KHesemeyer88/SDP/data/marcus_triangle.png

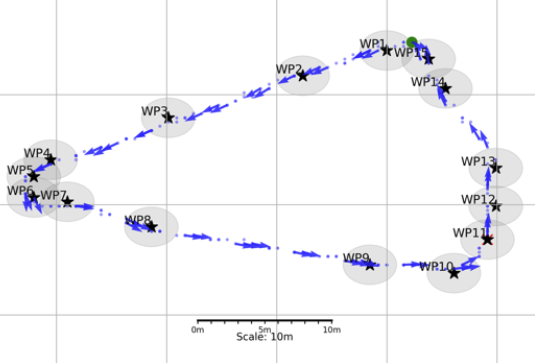
data/marcus_triangle.png
