KHesemeyer88/SDP/include/rtos_tasks.h

#ifndef RTOS_TASKS_H
#define RTOS_TASKS_H

#include <Arduino.h>
#include "freertos/FreeRTOS.h"
#include "freertos/task.h"
#include "freertos/queue.h"
#include "freertos/semphr.h"
#include "esp_task_wdt.h"
#include "http_server.h"
#include <ESP32Servo.h>

// Task priorities (1-24, higher number = higher priority)
#define CONTROL_TASK_PRIORITY       9
#define NAV_TASK_PRIORITY           8
#define GNSS_TASK_PRIORITY          10
#define OBSTACLE_TASK_PRIORITY      8
#define WEBSOCKET_TASK_PRIORITY     7
#define HTTP_SERVER_TASK_PRIORITY   6
#define LOG_TASK_PRIORITY           2

// Task stack sizes
#define CONTROL_TASK_STACK_SIZE     4096
#define WEBSOCKET_TASK_STACK_SIZE   20480
#define NAV_TASK_STACK_SIZE         4096
#define HTTP_SERVER_TASK_STACK_SIZE 8192
#define LOG_TASK_STACK_SIZE         4096
#define GNSS_TASK_STACK_SIZE        8192
#define OBSTACLE_TASK_STACK_SIZE    2048

// HTTP server task handle
extern TaskHandle_t httpServerTaskHandle;

// Forward declaration of HTTP server task
void HttpServerTask(void *pvParameters);

// Command types for the control queue
enum CommandType {
    CMD_MANUAL_CONTROL,
    CMD_AUTO_CONTROL,
    CMD_STOP
};

// Command structure for manual control
struct ManualControlCommand {
    float throttle;    // -1 to 1, negative is reverse
    float steering;    // -1 to 1, negative is left
    bool isDriving;    // Driving state flag
};

// Command structure for autonomous control
struct AutoControlCommand {
    float targetLat;
    float targetLon;
    bool followWaypoints;
};

// Union of all command types
struct ControlCommand {
    CommandType type;
    union {
        ManualControlCommand manual;
        AutoControlCommand autonomous;
    };
};

// Task handles
extern TaskHandle_t controlTaskHandle;
extern TaskHandle_t websocketTaskHandle;
extern TaskHandle_t obstacleTaskHandle;

// Mutex for accessing shared resources
extern SemaphoreHandle_t servoMutex;

// Queue for passing commands from WebSocket to control task
extern QueueHandle_t commandQueue;

// Servo objects
extern Servo steeringServo;
extern Servo escServo;

// Task functions
void ControlTask(void *pvParameters);
// WebSocket task now only handles periodic updates, not the WebSocket loop()
void WebSocketTask(void *pvParameters);

// Initialize all RTOS components
void initRTOS();

#endif // RTOS_TASKS_H
